hayashik/akagachi_eye_robot_hardware/Akagachi-1A/images/DSC00032.JPG

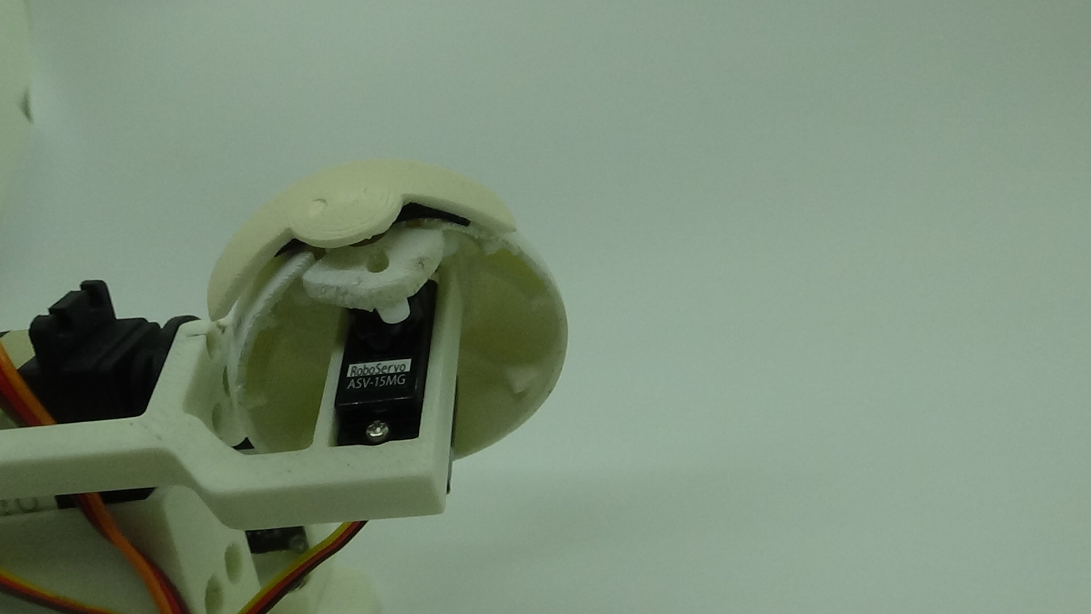
Akagachi-1A/images/DSC00032.JPG
